newHeiko/wiFred/documentation/quickstartLaser.adoc

= Quick instructions for wiFred
:icons: image
:iconsdir: /etc/asciidoc/images/icons/

include::quickBuild.adoc[tags=!drilljig]
include::quickStartup.adoc[]
