newHeiko/wiFred/hardware/beschriftungsvorlage.pdf

Charge << >> Full Stop Shift F0 F1 F2 F3F6 F5F8 F4F7 wiFred 2 3 Loco Loco4 1
