newHeiko/wiFred/hardware/beschriftungsvorlage_A4.pdf

ChargeFull

<< | >>
Stop | Shift

F0

F1 | F2 | F3
| F5 | F6

F8F7

F4

wiFred

2 | 3
Loco | Loco

41

ChargeFull

<< | >>
Stop | Shift

F0

F1 | F2 | F3
| F5 | F6

F8F7

F4

wiFred

2 | 3
Loco | Loco

41

ChargeFull

<< | >>
Stop | Shift

F0

F1 | F2 | F3
| F5 | F6

F8F7

F4

wiFred

2 | 3
Loco | Loco

41

ChargeFull

<< | >>
Stop | Shift

F0

F1 | F2 | F3
| F5 | F6

F8F7

F4

wiFred

2 | 3
Loco | Loco

41

ChargeFull

<< | >>
Stop | Shift

F0

F1 | F2 | F3
| F5 | F6

F8F7

F4

wiFred

2 | 3
Loco | Loco

41

ChargeFull

<< | >>
Stop | Shift

F0

F1 | F2 | F3
| F5 | F6

F8F7

F4

wiFred

2 | 3
Loco | Loco

41

ChargeFull

<< | >>
Stop | Shift

F0

F1 | F2 | F3
| F5 | F6

F8F7

F4

wiFred

2 | 3
Loco | Loco

41

ChargeFull

<< | >>
Stop | Shift

F0

F1 | F2 | F3
| F5 | F6

F8F7

F4

wiFred

2 | 3
Loco | Loco

41

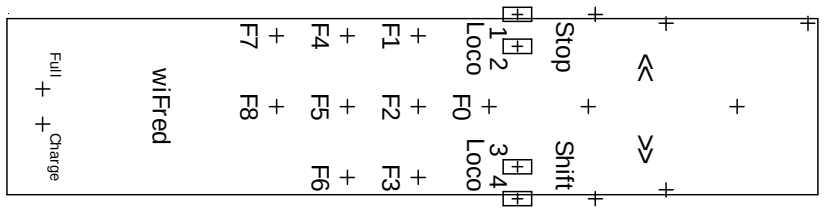
[picture p41: figure]
ChargeFull; Stop Shift; wiFred; Loco Loco 41
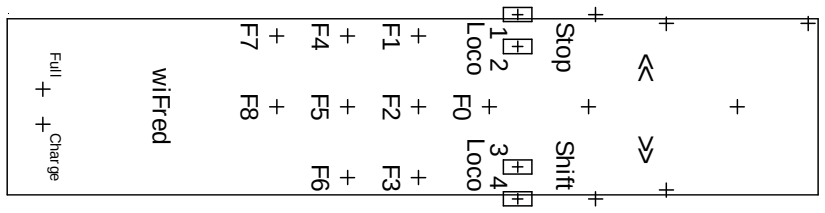
[picture p42: figure]
ChargeFull; Stop Shift; wiFred; Loco Loco 41
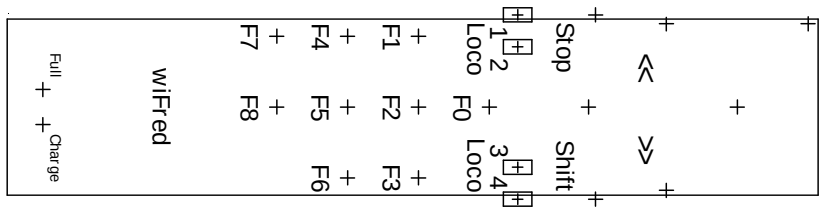
[picture p43: figure]
ChargeFull; Stop Shift; wiFred; Loco Loco 41
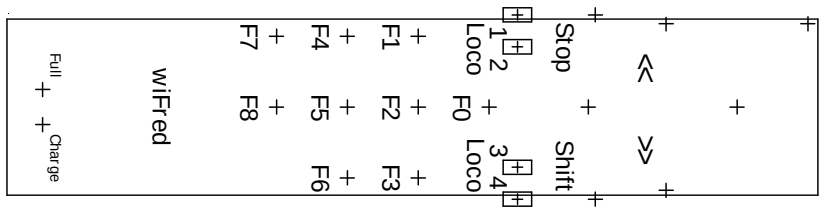
[picture p44: figure]
ChargeFull; Stop Shift; wiFred; Loco Loco 41
