newHeiko/wiFred/documentation/quickstartLaser.pdf

Quick instructions for wiFred | 1 / 2

## 1 Finish assembly (laser engraved enclosure)

1. Make cutout for micro USB connector
2. Install LEDs - long pin (positive) into square pad
- Red LEDs at D101 and D205/D301 with 3mm spacers
- Green LEDs at D102, D206/D302 and D207/D303 with 3mm spacers
- White LEDs at D208/D304 and D209/D305 - choose where and how long they should stick out of housing
3. Install potentiometer and loco selection switches
4. Install direction selection switch and connect pins to PCB with short wires or cutoffs from LEDs
5. Drill holes in enclosure - 3mm for LEDs, 3.5mm for push buttons, 6.5mm for direction switch, 8mm for potentiometer, 1.5mm for slide switches and carefully file slide switch slots to match switch handles
6. If push button switches are not installed: Place them on PCB (red at SW204, yellow at SW215) screw PCB into housing so they fit into the holes and solder them to the PCB
7. Connect battery to P101 - BATT-connector

Quick instructions for wiFred | 2 / 2
8. Arrange battery so it fits between direction selection switch and PCB screws and glue into back housing

Warning
Make sure red wire is connected to + and black wire connected to GND. Reversing the connection may destroy the wiFred.

Warning
Make sure nothing pinches the battery. LiIon batteries are susceptible to mechanical damage. == First startup
1. Charge device with a micro USB charger until charging LED switches to green
2. Turn on device with charger still connected (calibrates low battery threshold)
3. Wait for red LED on top to stop flashing and stay lit
4. Use any WiFi device to search for and connect to network wiFred-configXXXX
5. Connect to http://config.local and configure device

More information can be found at https://newHeiko.github.io/wiFred.
