newHeiko/wiFred/documentation/images/laptopComputer.png

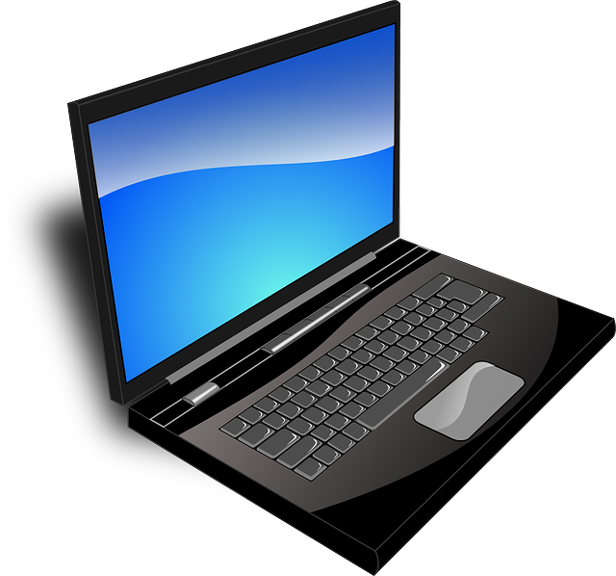
documentation/images/laptopComputer.png
