newHeiko/wiFred/documentation/images/screenShot_functions.png

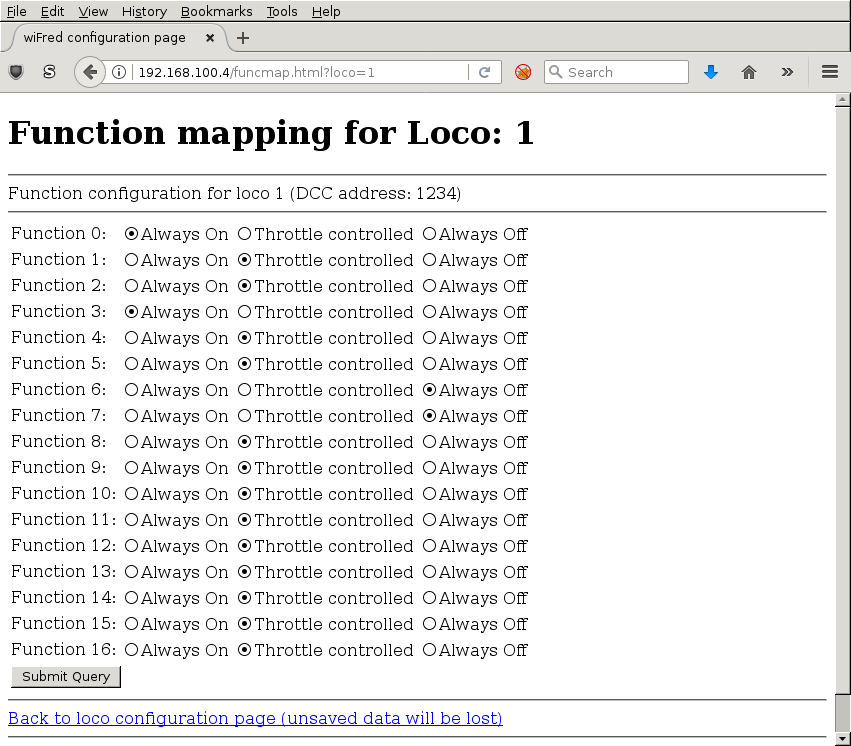
documentation/images/screenShot_functions.png
