newHeiko/wiFred/documentation/images/screenShot_main.png

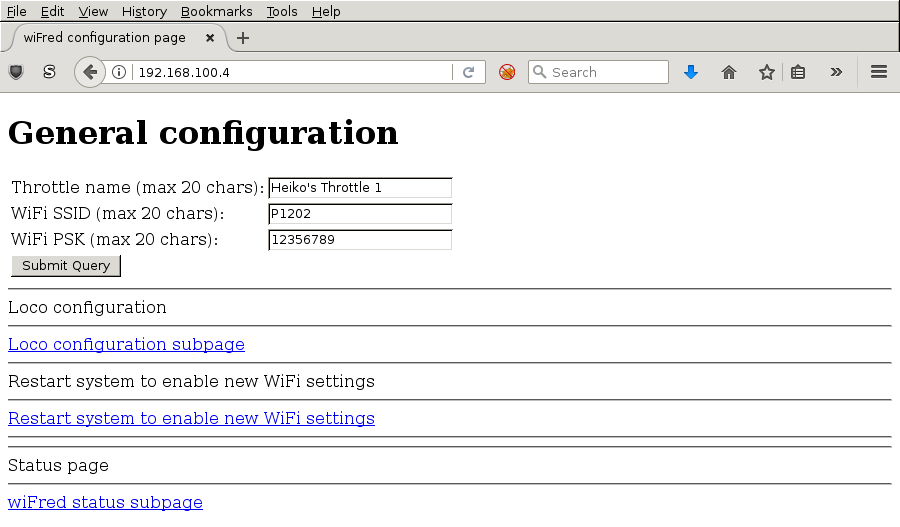
documentation/images/screenShot_main.png
