newHeiko/wiFred/documentation/images/screenShot_status.png

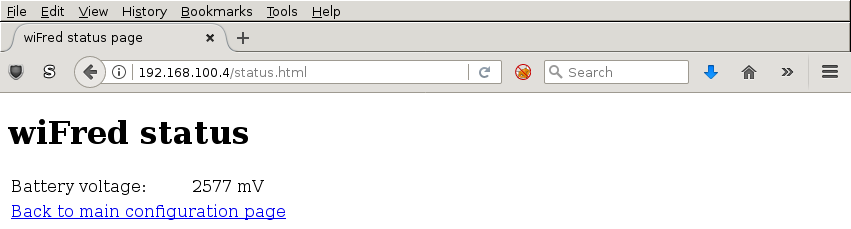
documentation/images/screenShot_status.png
