newHeiko/wiFred/documentation/images/smartphone-147656_640.png

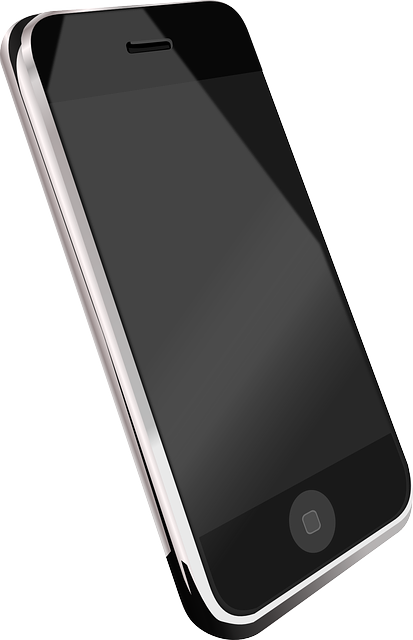
documentation/images/smartphone-147656_640.png
