newHeiko/wiFred/documentation/images/wifiRouter.png

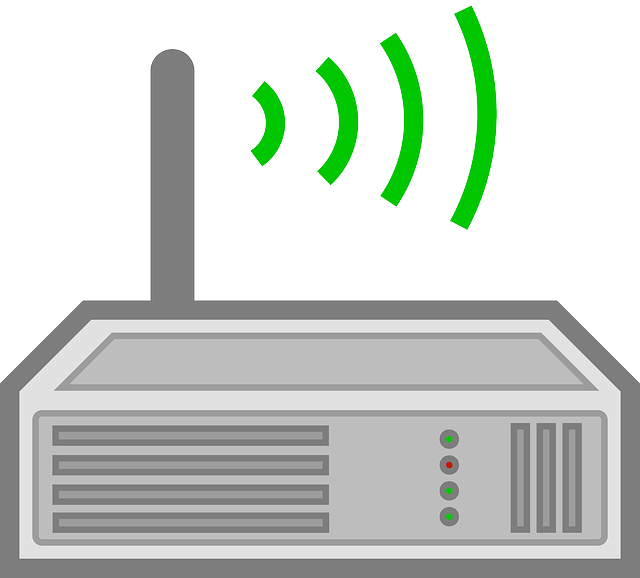
documentation/images/wifiRouter.png
