newHeiko/wiFred/software/esp-firmware/arduinoSettings.png

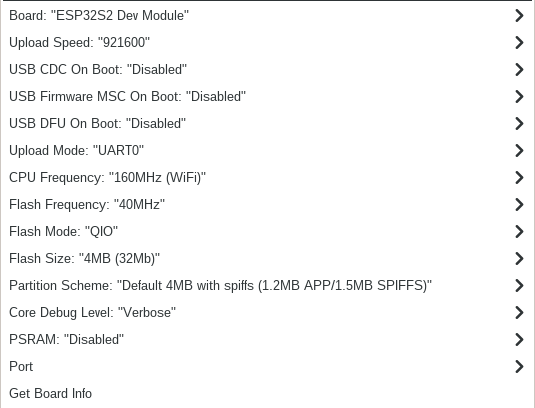
software/esp-firmware/arduinoSettings.png
