newHeiko/wiFred/documentation/largeImages/wfred-wifi_rev6-Wifi_connection.pdf

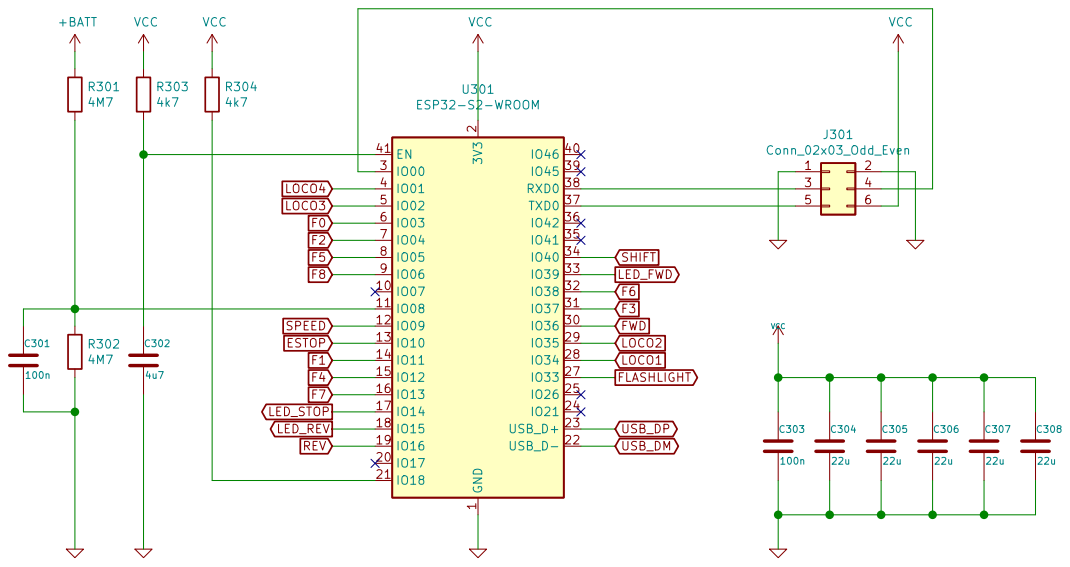
[picture p80: page 1]

LOCO4 LOCO3 F0F5F8 F2 SPEED | IO00 3

F7 ESTOP F4F1 LED_STOP LED_REV REV | IO09 12 IO10 13 IO11 14 IO12 15 IO13 16 IO14 17 IO15 18 IO17 20

WiFi controller and directly related peripheral stuff R302

File: wfred-wifi_rev6.sch Sheet: /Wifi connection/ Heiko Rosemann (heiko.rosemann@web.de) CC-BY-SA

Id: 3/3 Title: Wireless FREDI
