newHeiko/wiFred/documentation/largeImages/wfred_rev2.pdf

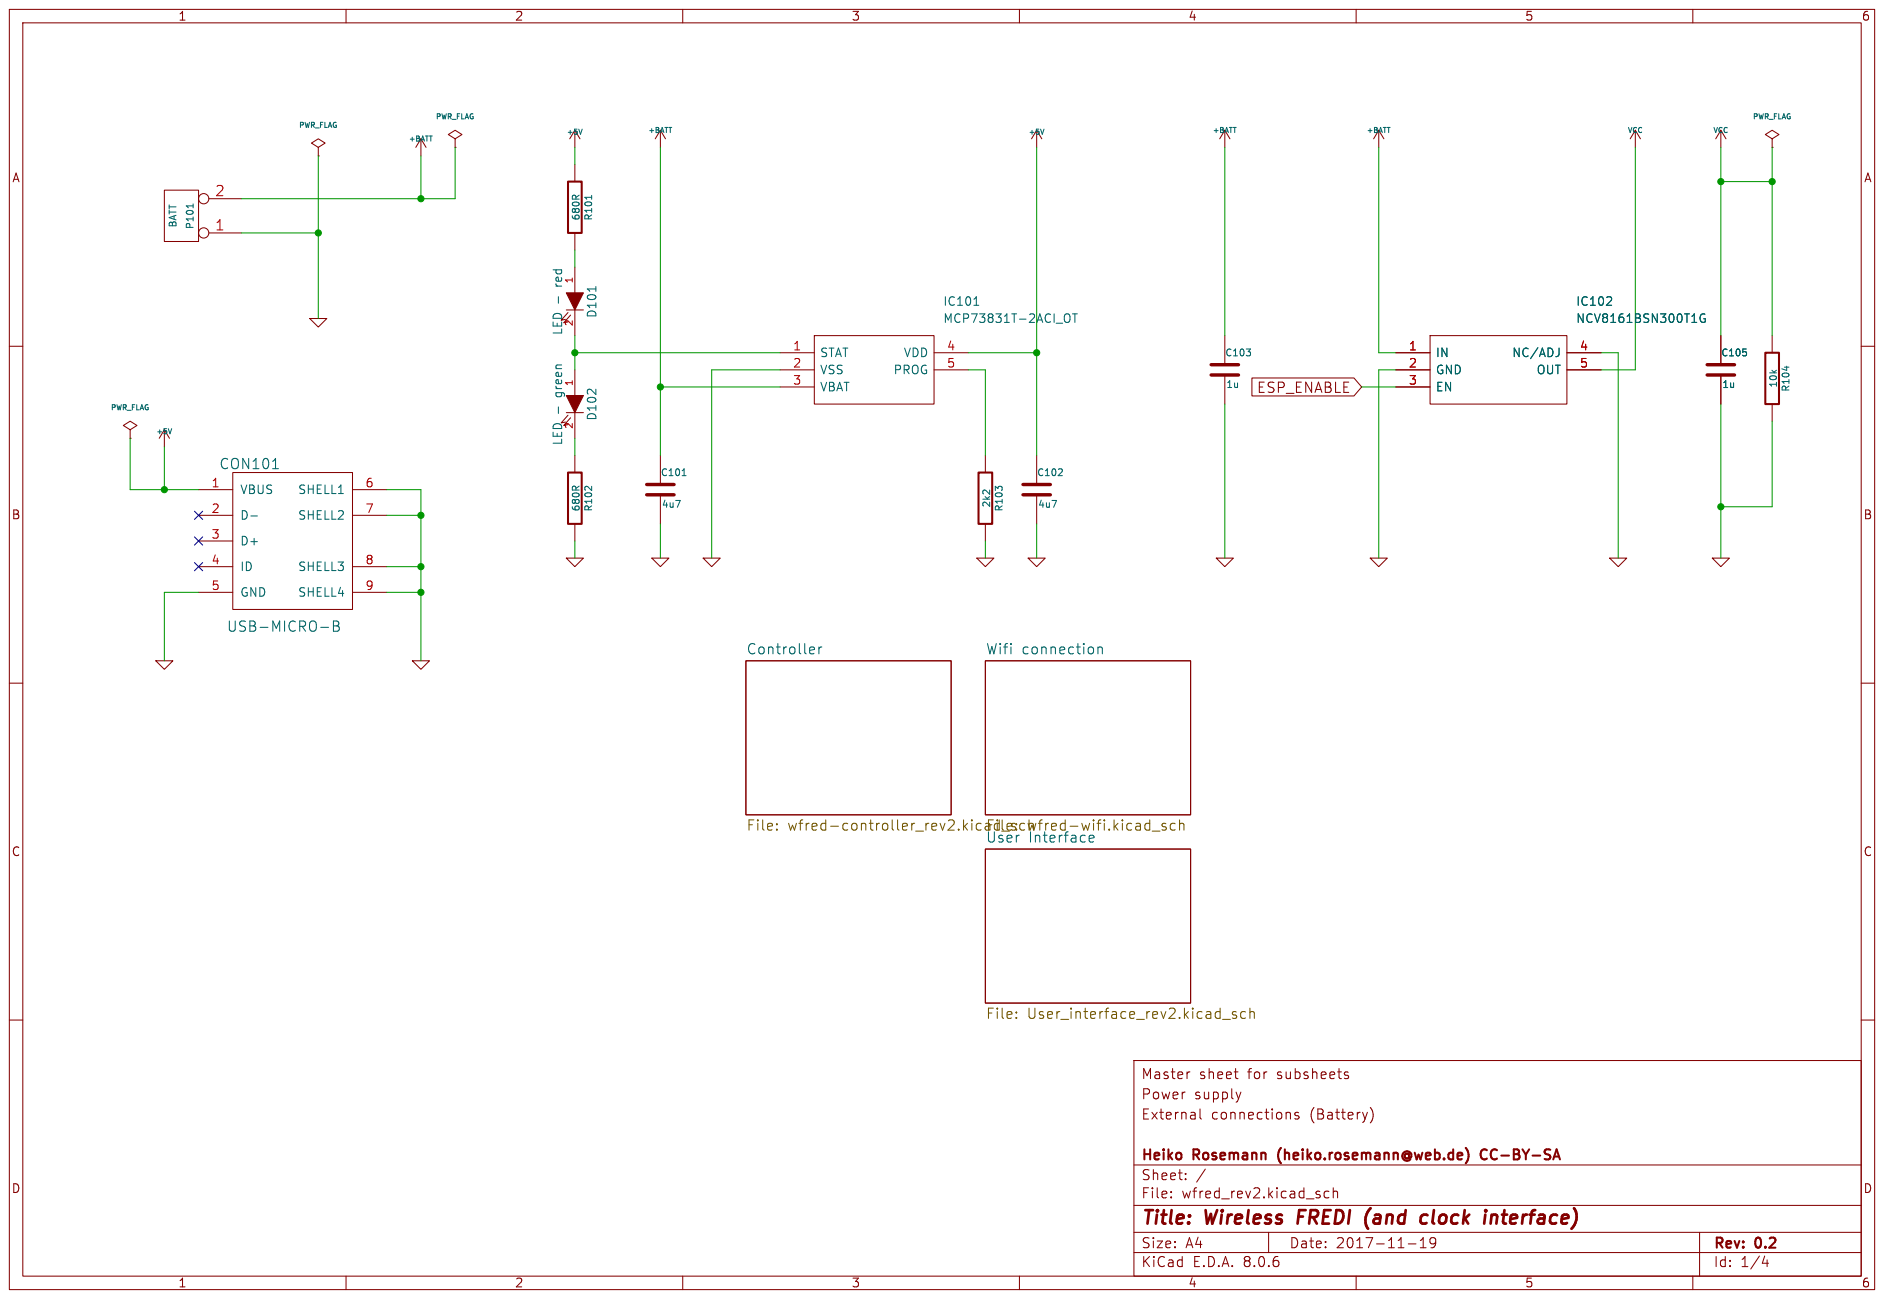
[picture p82: page 1]
