newHeiko/wiFred/documentation/largeImages/old_User_interface_rev2-User_Interface.pdf

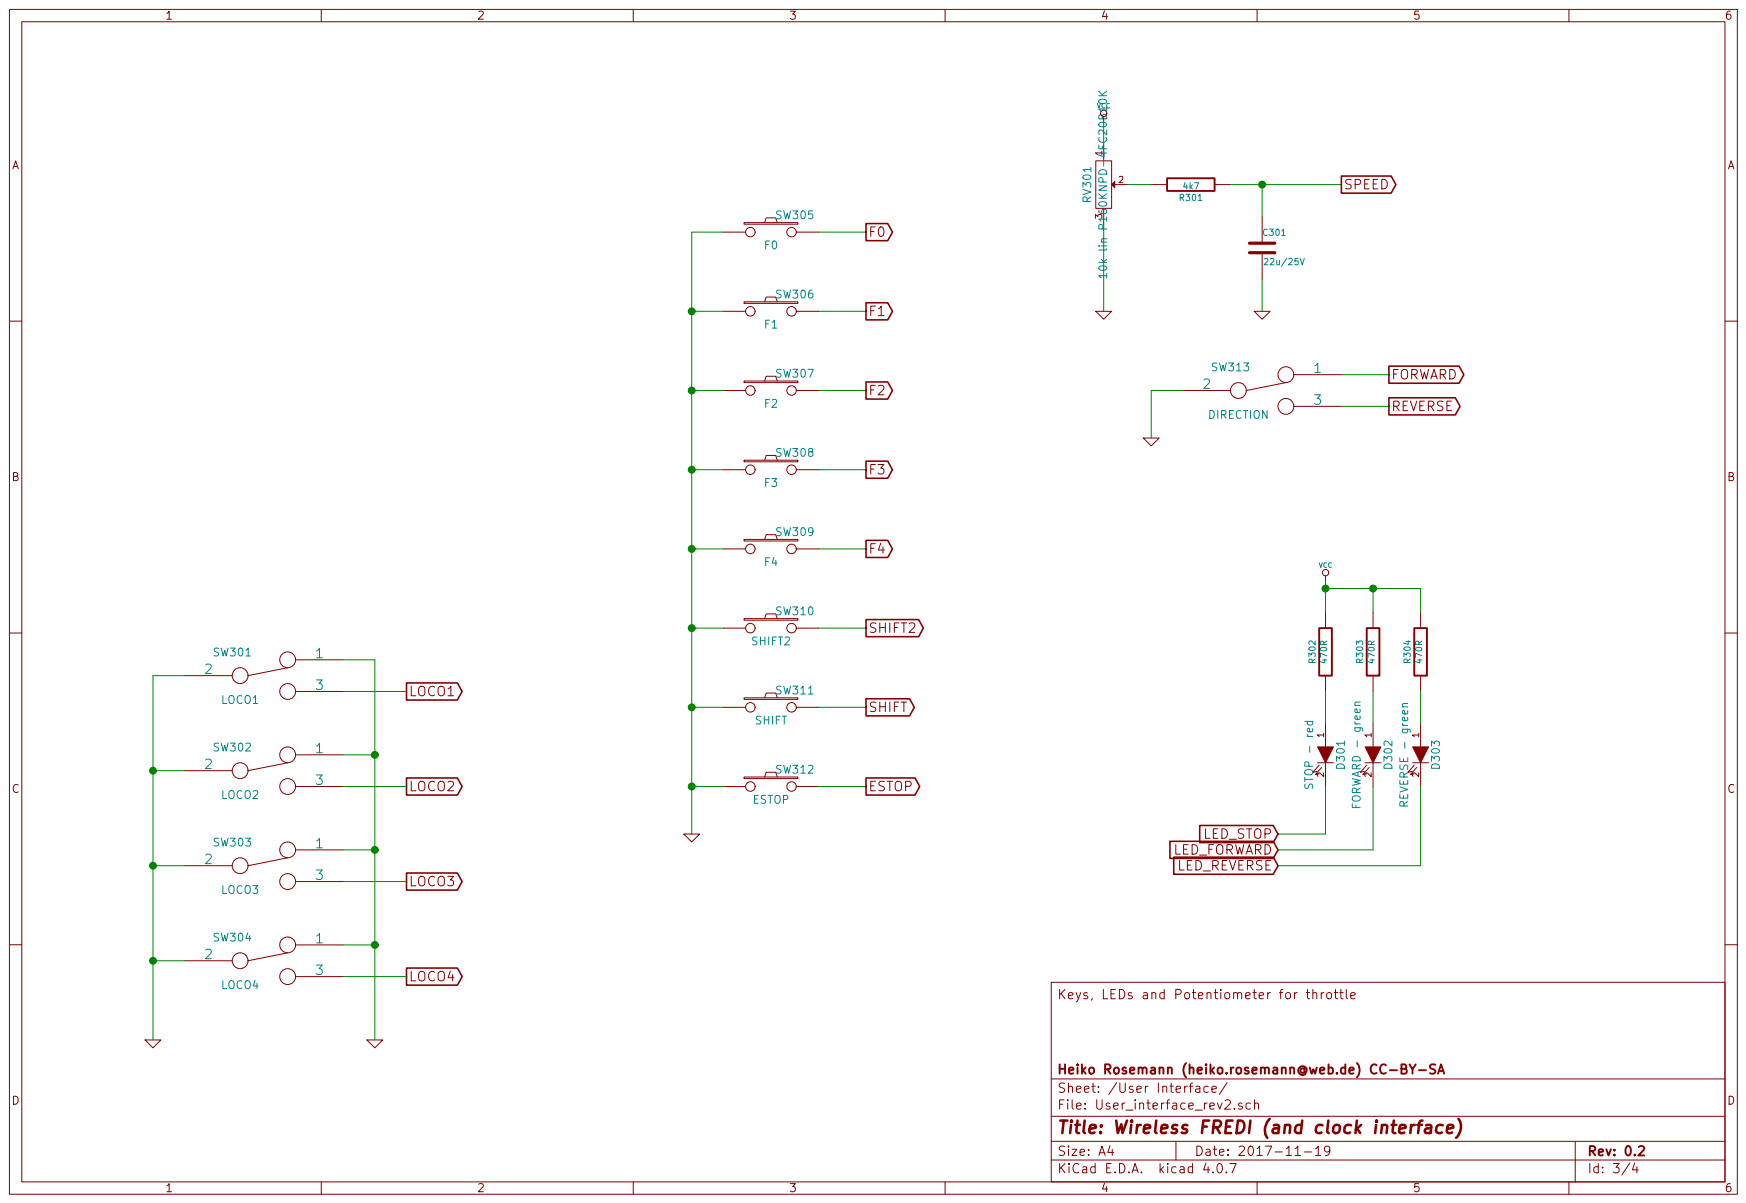
[picture p83: page 1]
