newHeiko/wiFred/documentation/largeImages/old_wfred-controller_rev2-Controller.pdf

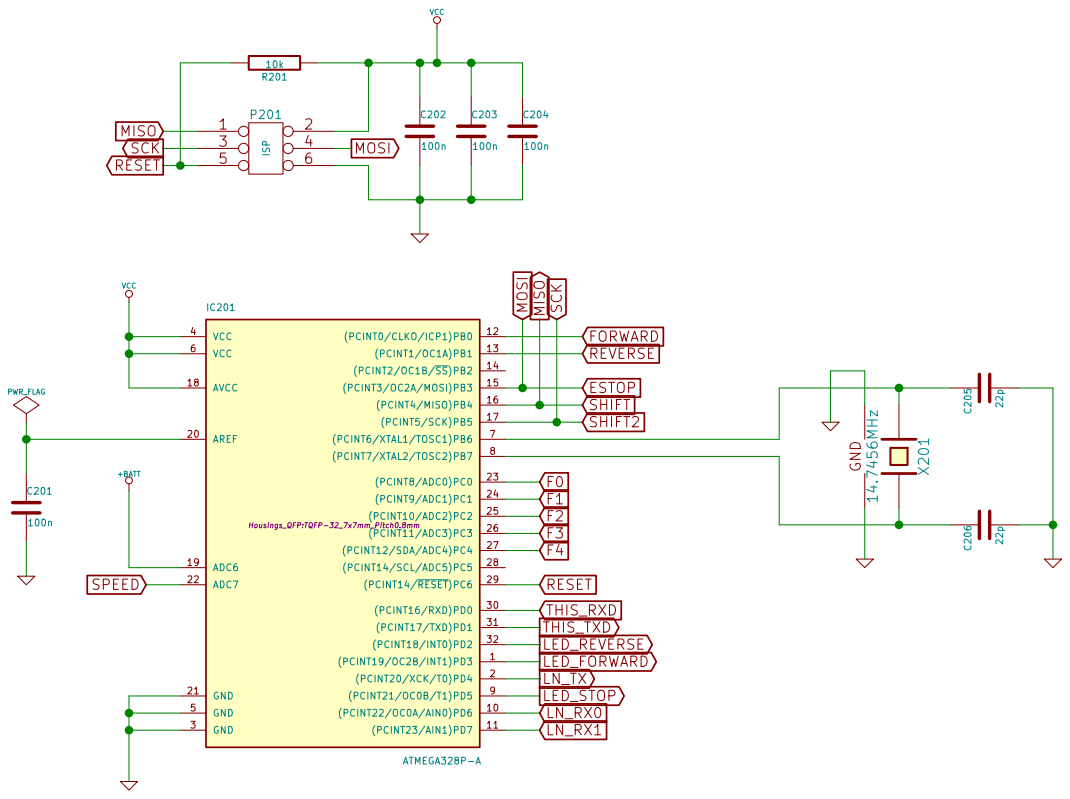
[picture p84: page 1]
