newHeiko/wiFred/documentation/largeImages/old_wfred-wifi-Wifi_connection.pdf

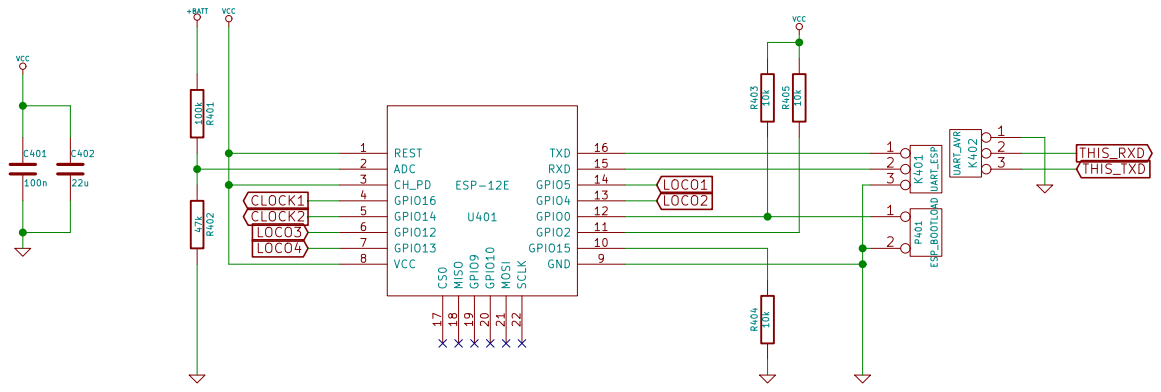
[picture p85: page 1]
