newHeiko/wiFred/documentation/largeImages/old_wfred_rev2.pdf

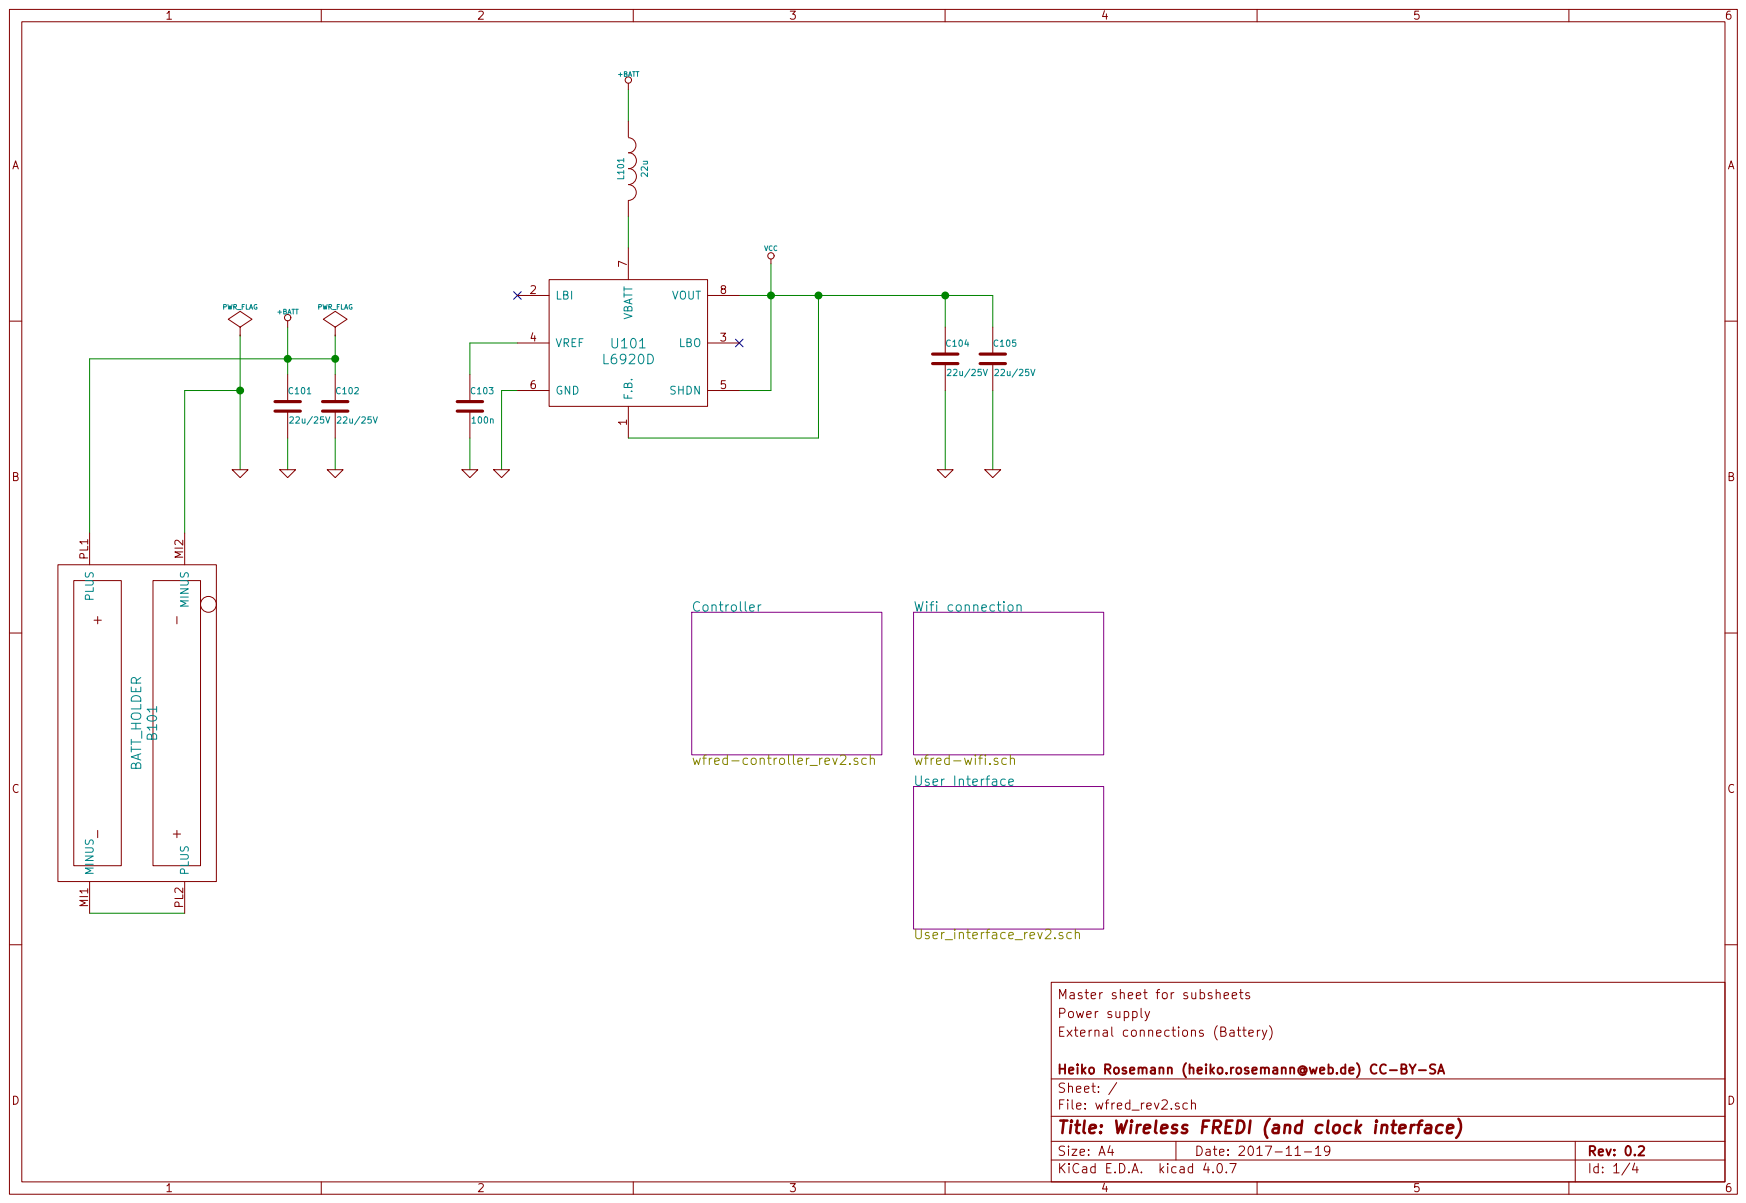
[picture p86: page 1]
